jmcpheron/pycon2026/docs/explainers/card-3d.md

# The card in 3D — assembly, exploded view, and parts

> The card lives in Onshape; the STEP export is the only thing committed at the repo root. Every visual on this page is built from that one file by a little Python script.

The model below is the literal AP242 STEP file exported from Onshape ([`jmcpheron-card.step`](https://github.com/jmcpheron/pycon2026/blob/main/jmcpheron-card.step)), routed through Python in three different ways:

1. **`cascadio`** converts STEP → GLB in one call, keeping Onshape's per-part colors (the deep-blue gears and gray card halves you see below).
2. **`trimesh`** splits the assembly into seven named parts and writes one GLB + STL + PNG per part.
3. **OpenSCAD**, driven from Python, renders the per-frame exploded-view animation further down the page.

All three are wired together by `uv run cardlab explode --in jmcpheron-card.step --out docs/assets/card/`.

## Assembly

<script type="module" src="https://ajax.googleapis.com/ajax/libs/model-viewer/4.0.0/model-viewer.min.js"></script>

<model-viewer src="../assets/card/jmcpheron-card.glb"
              alt="Reduction gear business card, fully assembled — five blue 40-tooth spur gears between two light-gray card halves"
              camera-controls auto-rotate ar
              shadow-intensity="1"
              exposure="1"
              style="width:100%;height:480px;background:#faf7e8;border-radius:6px">
</model-viewer>

That's a `<model-viewer>` element pointed at the cascadio-produced GLB. Drag to orbit, scroll to zoom. On a phone you can tap the AR icon to drop the card on a real surface.

## Exploded view

The card-layered explode strategy lifts the two card halves to ±25 mm on Z and fans the five gears between them, sorted by their X position. The bottom card's shaft-hole pattern becomes visible — five holes spaced 15 mm apart, which is the gear-train pitch.

exploded card animation — top card half lifted, gear train staggered between, bottom card half lowered

## Parts

There are seven instances of three distinct parts. Both card halves share the name "Part 1" in Onshape; the five gears all share "Spur gear (40 teeth)" — but two of them are actually a **tall-hub variant** for the compound stages (8 mm Z extent vs the standard 3 mm). The renders make the distinction visible at a glance.

<div class="parts-gallery">
<!-- One <figure> per entry in manifest.toml — populated by hand for now;
     the explainers tool will generate this section in a follow-up so it
     stays in sync with re-exports. -->
</div>

The full part list (with centroids, bounding boxes, displacement vectors, and any sidecar gear-ratio metadata) lives in [`manifest.toml`](../assets/card/manifest.toml).

## What's lost in the STEP export

Onshape's STEP exporter is faithful about geometry and colors. It's quiet about everything else:

- **Tooth counts and gear ratios** don't survive as structured properties — only as substrings in part names like `Spur gear (40 teeth)`. The ratio chain documented in [gear-ratios](gear-ratios.md) comes from [`card.py`](../../src/explainers/card.py), not from the STEP.
- **Mate connectors** survive as nameless `AXIS2_PLACEMENT_3D` placement frames. You can recover the *positions* (we do — each gear's centroid in the manifest), but not the *kind* of mate (concentric, planar, distance-along-axis).
- **Feature history** is irrelevant for a B-rep export — STEP is the result, not the recipe.

If you want any of these back in the loop, commit a sidecar `jmcpheron-card.meta.toml` next to the STEP. `cardlab inspect` merges it into the report; `cardlab explode` joins it to each rendered part by name.

There's also a different recovery path: **derive what was lost from the geometry itself**. The [decoding-gears explainer](decoding-gears.md) slices one of the gear STLs, FFTs the radial profile to recover the tooth count empirically (40 for the disc, 10 for the pinion), back-solves the module from the outer diameter, and reconstructs the 256:1 chain — then asks what happens if you roll the card along the floor like a measuring tape.

---

*Generated by `uv run cardlab explode`. The MkDocs-free page is on purpose — GitHub Pages renders this markdown directly, and `<model-viewer>` is the only client-side dep.*
