jmcpheron/pycon2026/docs/explainers/index.md

# Engineering writeups for the gear card

> *[your voice here] one paragraph framing the project: a 3D-printed business card with a 256:1 compound reduction-gear chain, and a Python-driven repo that explains the engineering behind it.*

This directory is a *generated* set of writeups. Every page below is produced by running a Python script in [`src/explainers/`](../../src/explainers). The math, diagrams, and tables come from one parameter file ([`card.py`](../../src/explainers/card.py)) — change a number there and every page reflects it on the next build.

```
src/explainers/<topic>.py  ─►  uv run explainers build <topic>  ─►  docs/explainers/<topic>.md (+ assets/*.svg)
```

## The six sections

### 1. [Gear ratios](gear-ratios.md)

How 5 compound gears at 4:1 each compound to 256:1, and how that translates to your thumb walking metres of arc per output rotation. Bar chart of cumulative ratio per stage; line chart of thumb travel distance.

### 2. [Stacking and interleaving](stacking.md)

The actual engineering puzzle: how do you fit 5 compound gears in a 5 mm card without their big discs colliding? Three side-view cross-sections walk through the failure modes and the eventual 3-level cycle that solves it.

### 3. [Terminology](terminology.md)

Pinion vs big gear, hub vs boss, post vs axle vs arbor. One annotated cross-section labels every named feature; a glossary table covers the rest.

### 4. [3D-printing considerations](printing.md)

Print orientation, the hub-to-pinion overhang and why a 45° chamfer fixes it, and why the post is its own part rather than printed monolithic with the gear.

### 5. [The card in 3D](card-3d.md)

The Onshape STEP itself, pulled apart by Python. An interactive `<model-viewer>` embed, an exploded-view animation, and per-part renders — all built from the one [`jmcpheron-card.step`](../../jmcpheron-card.step) by `cardlab explode`.

### 6. [Decoding the gears from STEP](decoding-gears.md)

Onshape's STEP export drops the parametric metadata — we recover it from the committed STL by slicing the gear, FFT-ing the radial profile, and back-solving the module. Plus a rolling-tape thought experiment: how far do you push the card before the output ticks once?

## Why a Python repo, not a static site?

Each explainer is a small Python script. You can read its source, change a parameter, re-run it, and the writeup updates. The diagrams aren't hand-drawn — they're [SVG primitives](../../src/explainers/diagrams.py) composed by Python from the same inputs. The repo is the explanation.

CI rebuilds these pages on every push that touches [`src/explainers/`](../../src/explainers) and auto-commits the regenerated markdown + SVG, so what you're reading on github.com is always the result of running today's source.

---

*Generated by [`src/explainers/index.py`](../../src/explainers/index.py).*
