jmcpheron/pycon2026/output/run-20260507T053409Z/iter-00/render.png

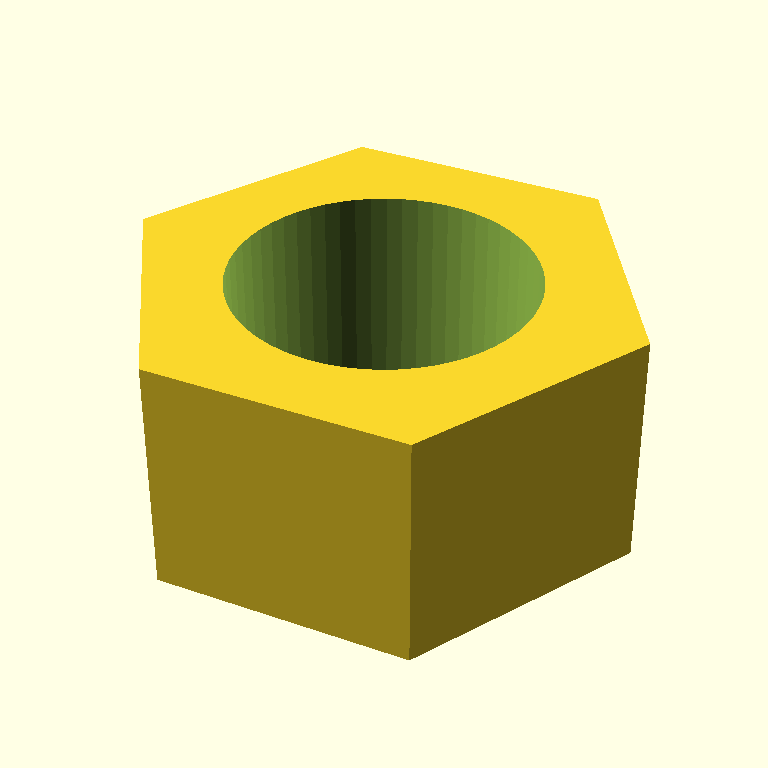
output/run-20260507T053409Z/iter-00/render.png
