jmcpheron/pycon2026/output/run-20260507T072032Z/iter-00/render.png

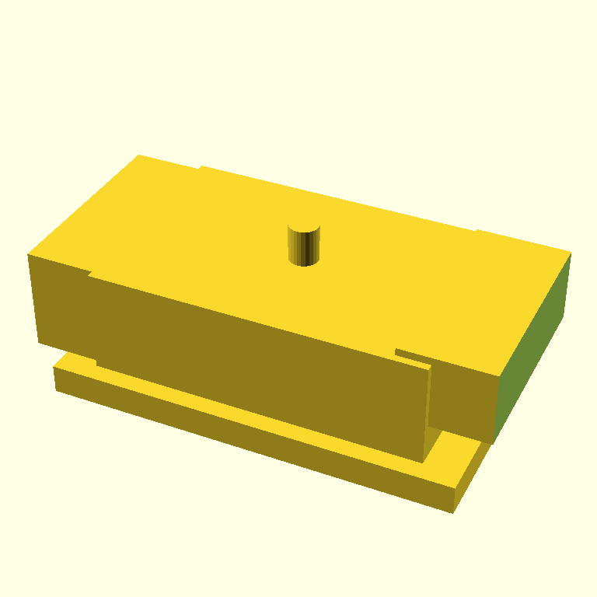
output/run-20260507T072032Z/iter-00/render.png
