jmcpheron/pycon2026/output/run-20260507T075931Z/iter-00/render.png

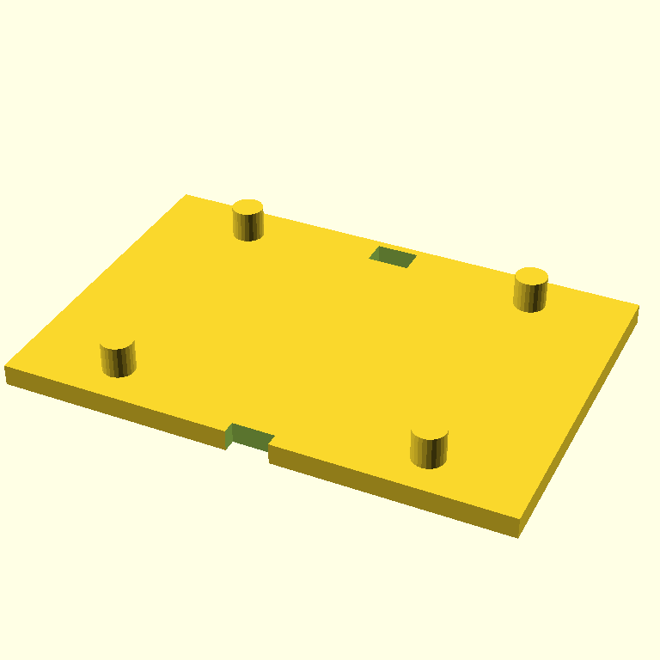
output/run-20260507T075931Z/iter-00/render.png
