jmcpheron/pycon2026/output/run-20260507T144420Z/iter-00/render.png

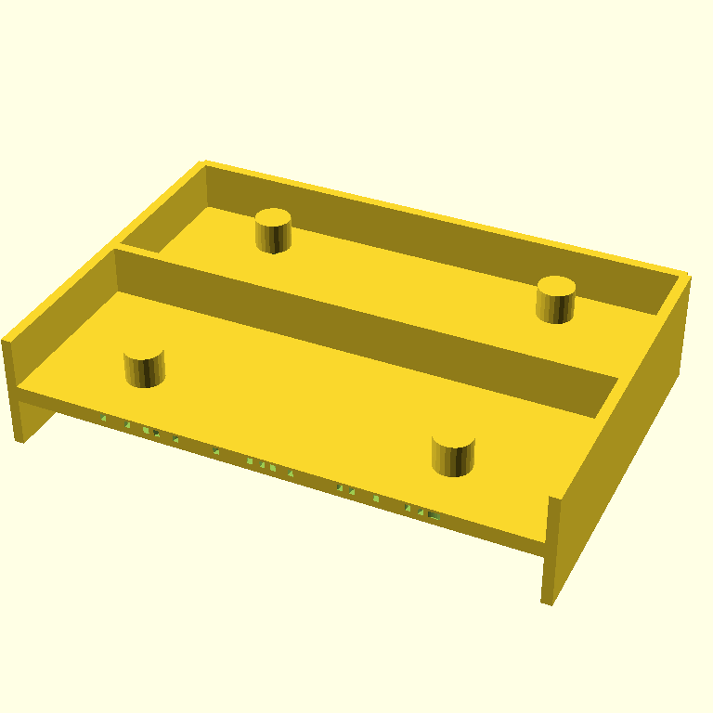
output/run-20260507T144420Z/iter-00/render.png
