jmcpheron/pycon2026/output/run-20260507T144420Z/iter-01/render.png

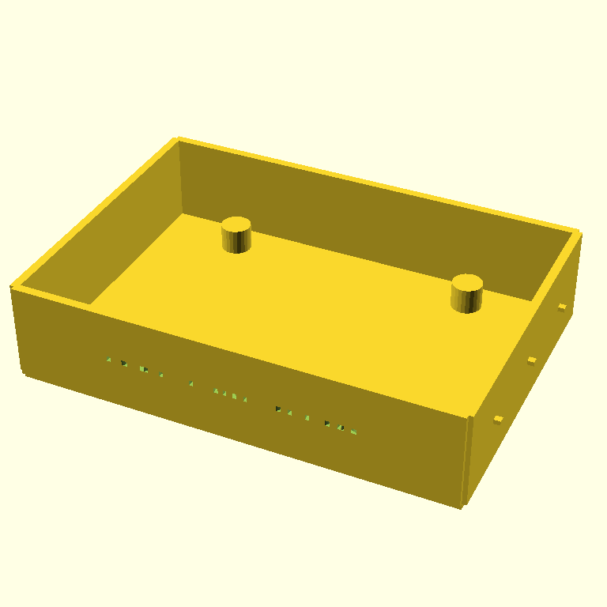
output/run-20260507T144420Z/iter-01/render.png
