jmcpheron/pycon2026/output/smoketest/cube.png

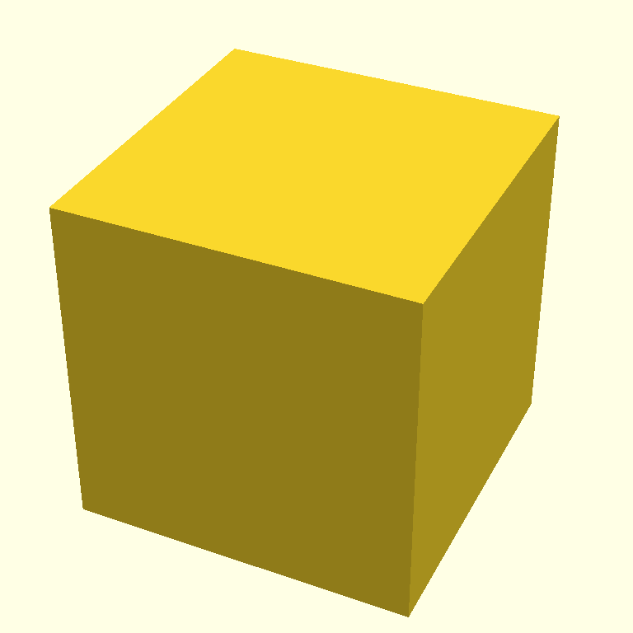
output/smoketest/cube.png
