jmcpheron/pycon2026/docs/pounce-a-pult/assets/parts/Part_1_3.stl

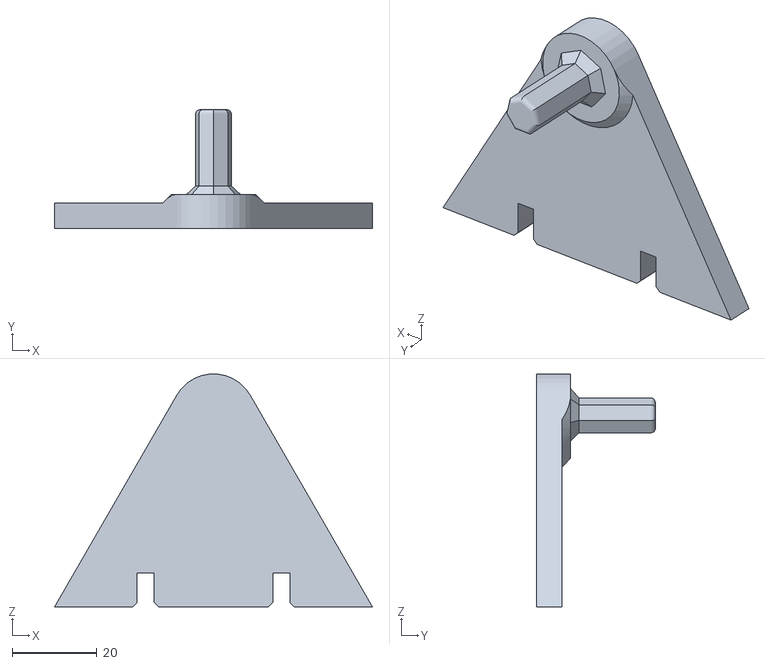
[picture p44: CAD file, 2026-05-15]
docs/pounce-a-pult/assets/parts/Part_1_3.stl
75.1 x 28.0 x 55.0
