jmcpheron/pycon2026/docs/vault/assets/parts/rack.stl

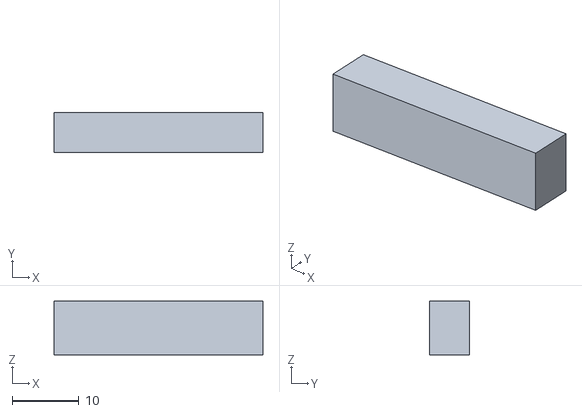
[picture p45: CAD file, 2026-05-16]
docs/vault/assets/parts/rack.stl
31.2 x 5.98 x 8.00
