jmcpheron/pycon2026/docs/vault/sandbox/ring_gear.stl

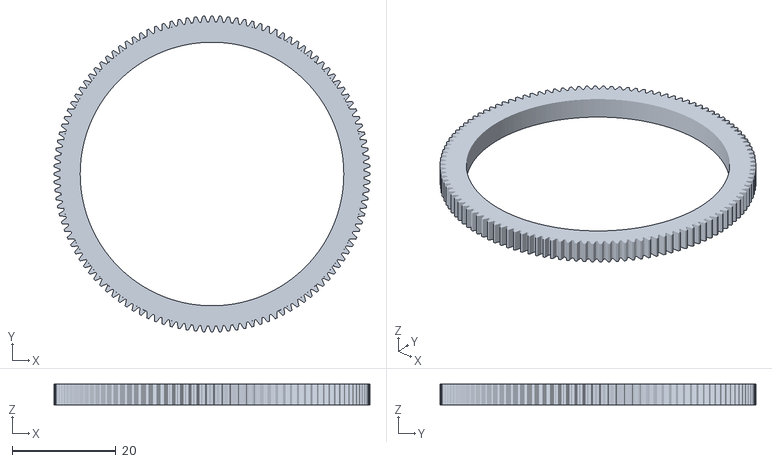
[picture p46: CAD file, 2026-05-19]
docs/vault/sandbox/ring_gear.stl
61.0 x 61.0 x 4.00
