jmcpheron/pycon2026/step-demo/parts/base.step

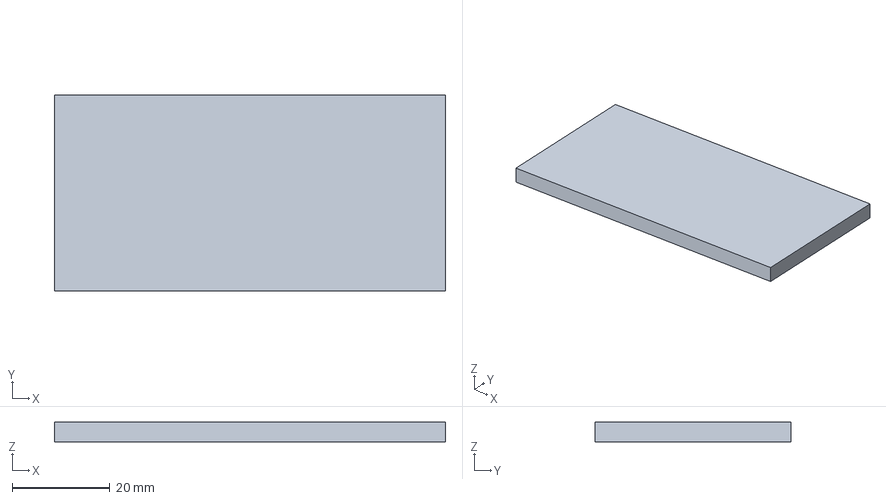
[picture p47: CAD file, 2026-05-17]
step-demo/parts/base.step
80.0 x 40.0 x 4.00 mm
