jmcpheron/pycon2026/docs/pounce-a-pult/assets/parts/Part_1_1.stl

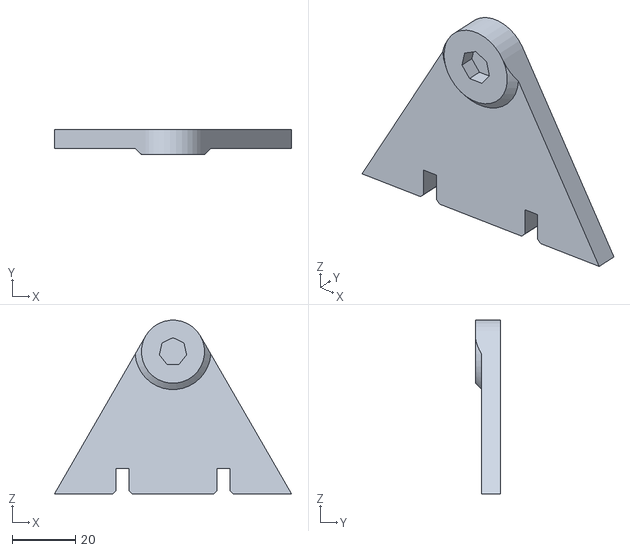
[picture p48: CAD file, 2026-05-15]
docs/pounce-a-pult/assets/parts/Part_1_1.stl
75.1 x 8.00 x 55.0
