jmcpheron/pycon2026/docs/vault/assets/parts/spur-gear.stl

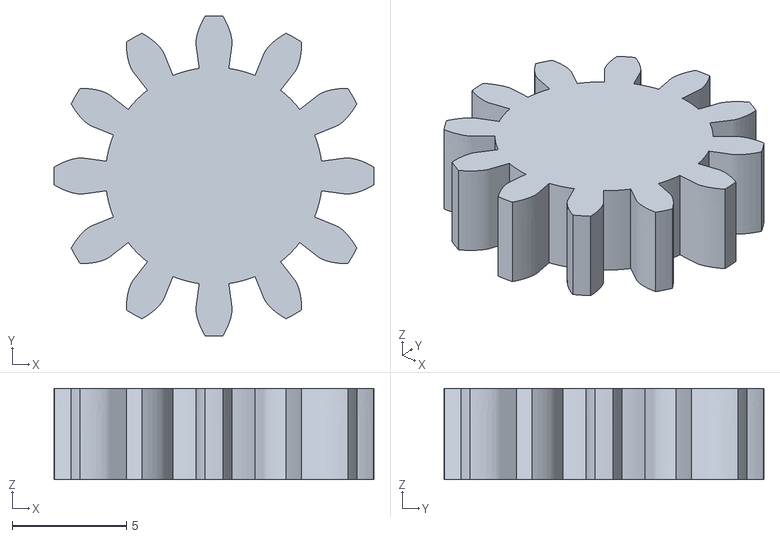
[picture p49: CAD file, 2026-05-16]
docs/vault/assets/parts/spur-gear.stl
14.0 x 14.0 x 4.00
