jmcpheron/pycon2026/step-demo/parts/arm.step

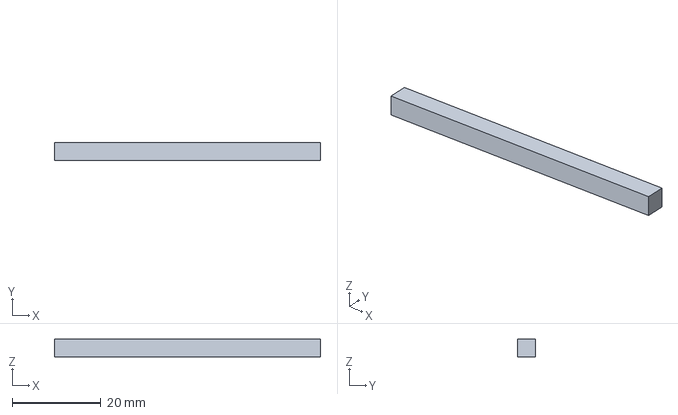
[picture p50: CAD file, 2026-05-17]
step-demo/parts/arm.step
60.0 x 4.00 x 4.00 mm
