jmcpheron/pycon2026/docs/pounce-a-pult/assets/parts/Part_1_2.stl

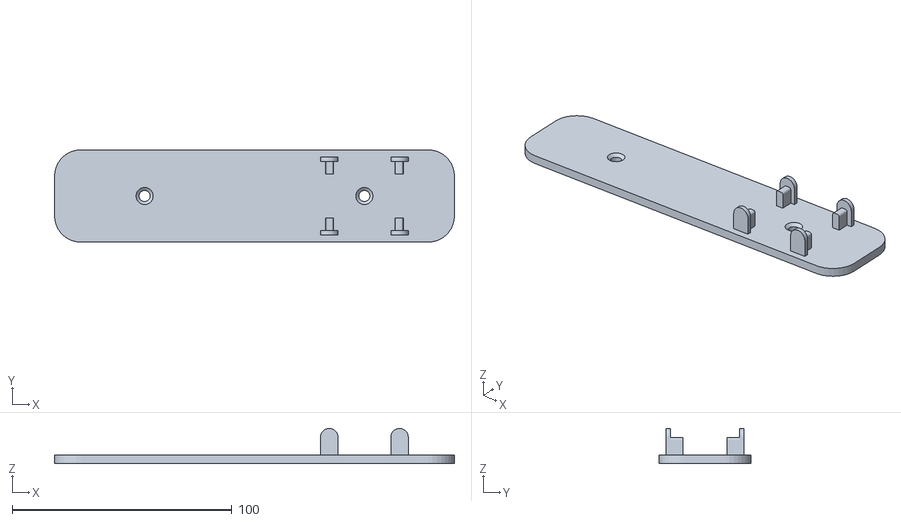
[picture p51: CAD file, 2026-05-15]
docs/pounce-a-pult/assets/parts/Part_1_2.stl
182.0 x 42.0 x 16.0
