jmcpheron/pycon2026/docs/vault/assets/parts/door-rim.stl

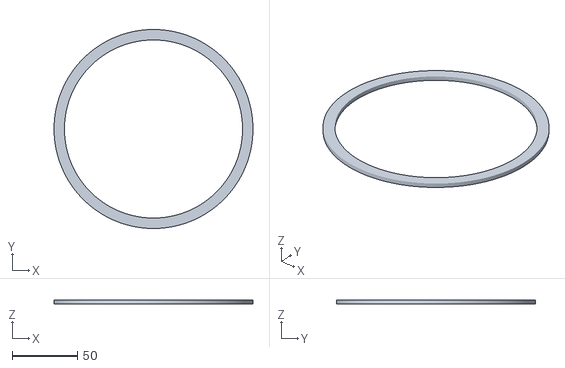
[picture p52: CAD file, 2026-05-16]
docs/vault/assets/parts/door-rim.stl
152.4 x 152.4 x 3.00
