jmcpheron/pycon2026/step-demo/parts/cup.step

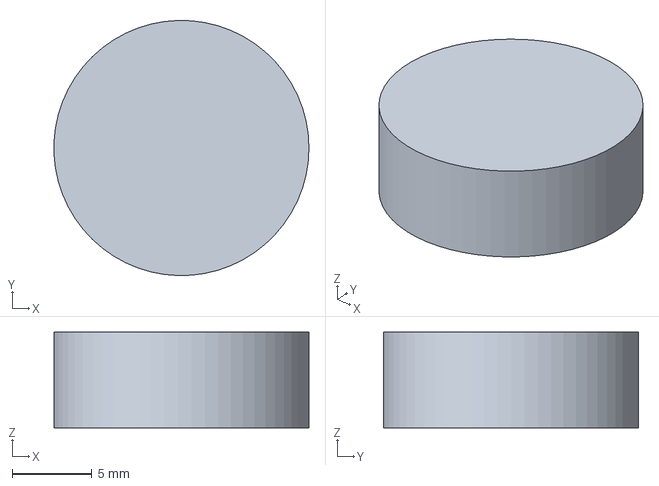
[picture p53: CAD file, 2026-05-17]
step-demo/parts/cup.step
16.0 x 16.0 x 6.00 mm
