jmcpheron/pycon2026/docs/assets/card/parts/Spur_gear_40_teeth_4.stl

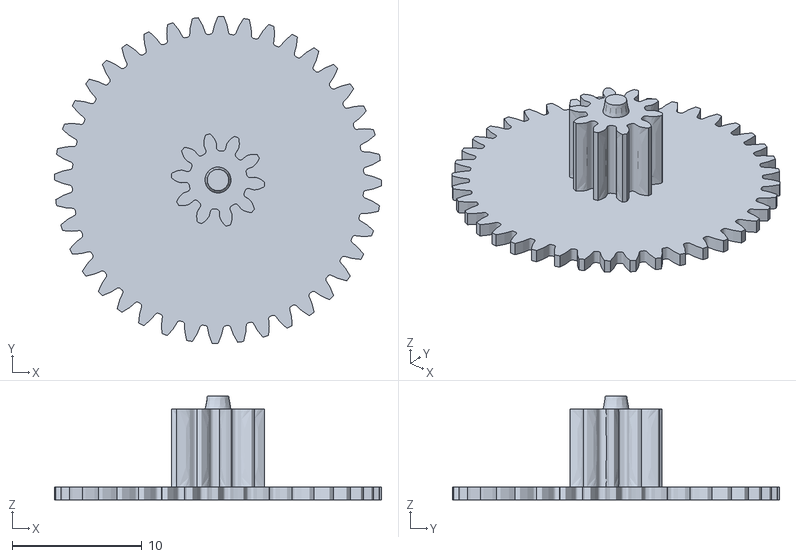
[picture p54: CAD file, 2026-05-13]
docs/assets/card/parts/Spur_gear_40_teeth_4.stl
25.2 x 25.2 x 8.00
