jmcpheron/pycon2026/docs/pounce-a-pult/assets/parts/Part_1_5.stl

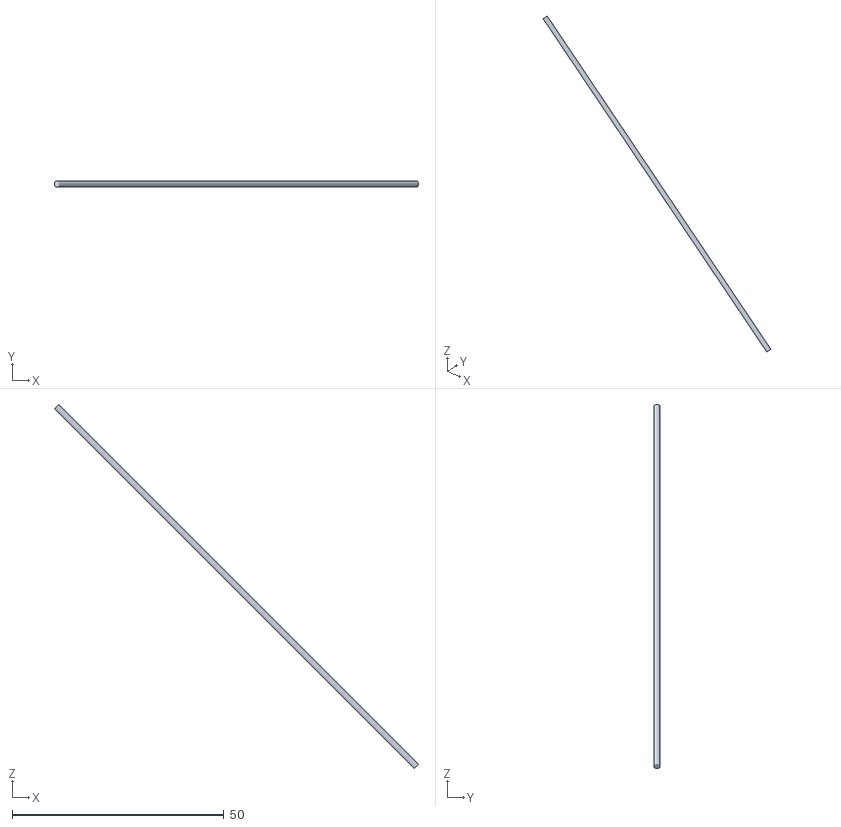
[picture p55: CAD file, 2026-05-15]
docs/pounce-a-pult/assets/parts/Part_1_5.stl
85.9 x 1.49 x 85.9
