jmcpheron/pycon2026/docs/vault/assets/parts/pin.stl

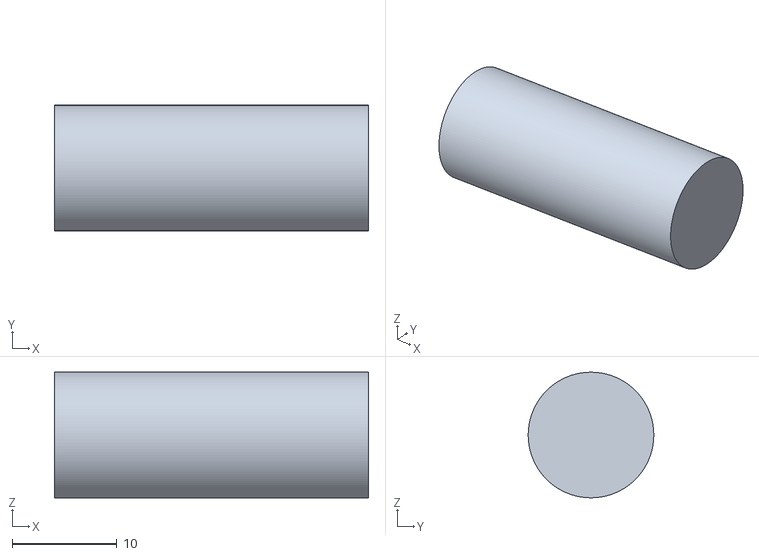
[picture p56: CAD file, 2026-05-16]
docs/vault/assets/parts/pin.stl
30.0 x 12.0 x 12.0
