jmcpheron/pycon2026/docs/pounce-a-pult/assets/parts/Part_1_4.stl

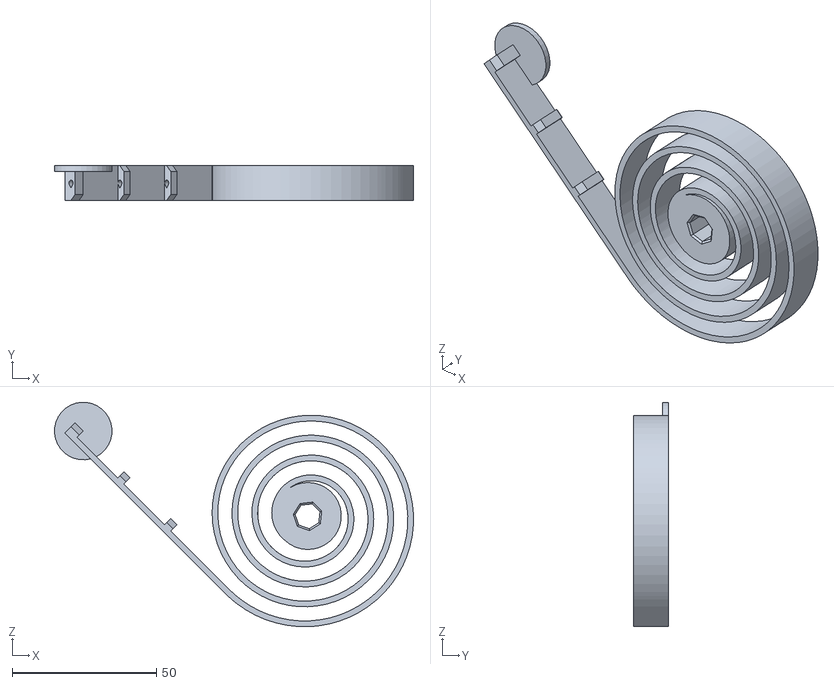
[picture p57: CAD file, 2026-05-15]
docs/pounce-a-pult/assets/parts/Part_1_4.stl
124.6 x 12.0 x 77.9
