jmcpheron/pycon2026/docs/assets/card/parts/Part_1.stl

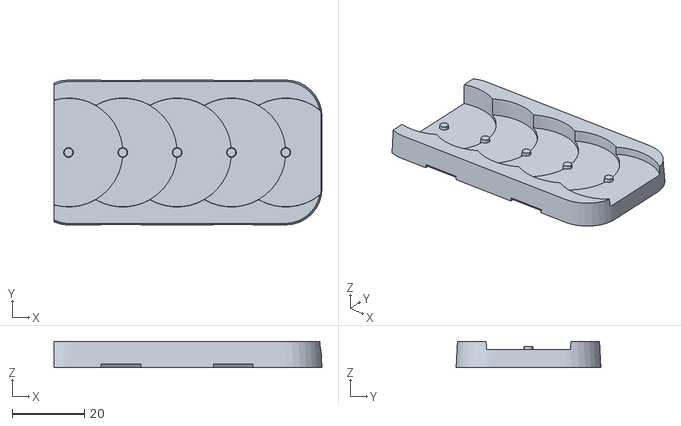
[picture p58: CAD file, 2026-05-13]
docs/assets/card/parts/Part_1.stl
74.0 x 40.0 x 7.30
