jmcpheron/pycon2026/output/smoketest/cube.scad

cube([20, 20, 20], center=true);
