jmcpheron/pycon2026/output/experiments/multi-gen-2026-05-07-anvil/anthropic_claude-haiku-4.5.png

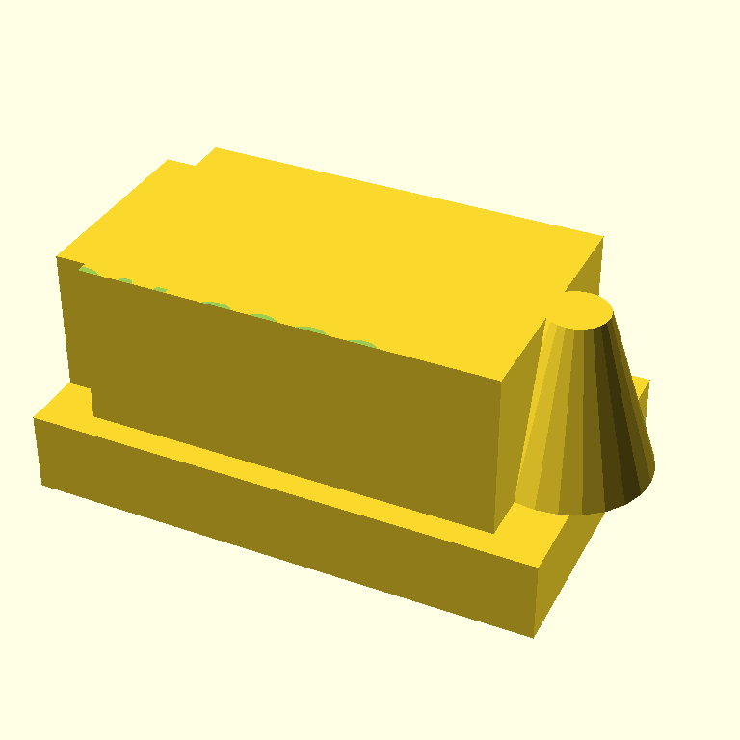
output/experiments/multi-gen-2026-05-07-anvil/anthropic_claude-haiku-4.5.png
