jmcpheron/pycon2026/output/experiments/multi-gen-2026-05-07-anvil/google_gemini-2.5-flash.png

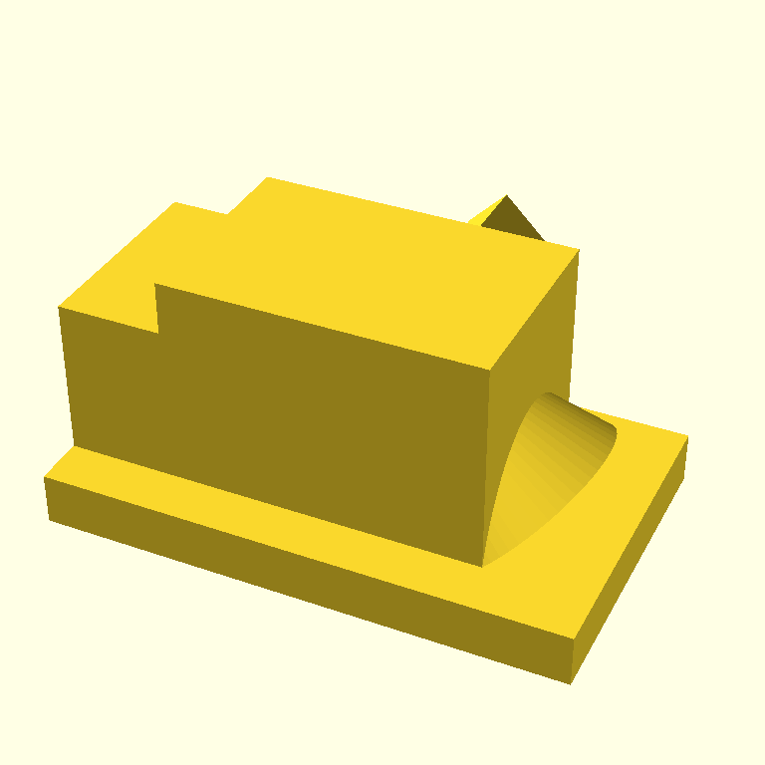
output/experiments/multi-gen-2026-05-07-anvil/google_gemini-2.5-flash.png
