jmcpheron/pycon2026/output/experiments/multi-gen-2026-05-07-anvil/google_gemma-4-31b-it.png

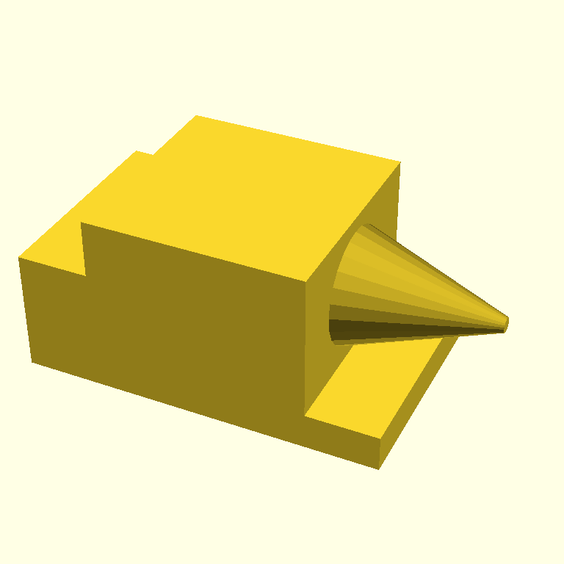
output/experiments/multi-gen-2026-05-07-anvil/google_gemma-4-31b-it.png
